kearwood/arcade/base/drop-sheet.jpg

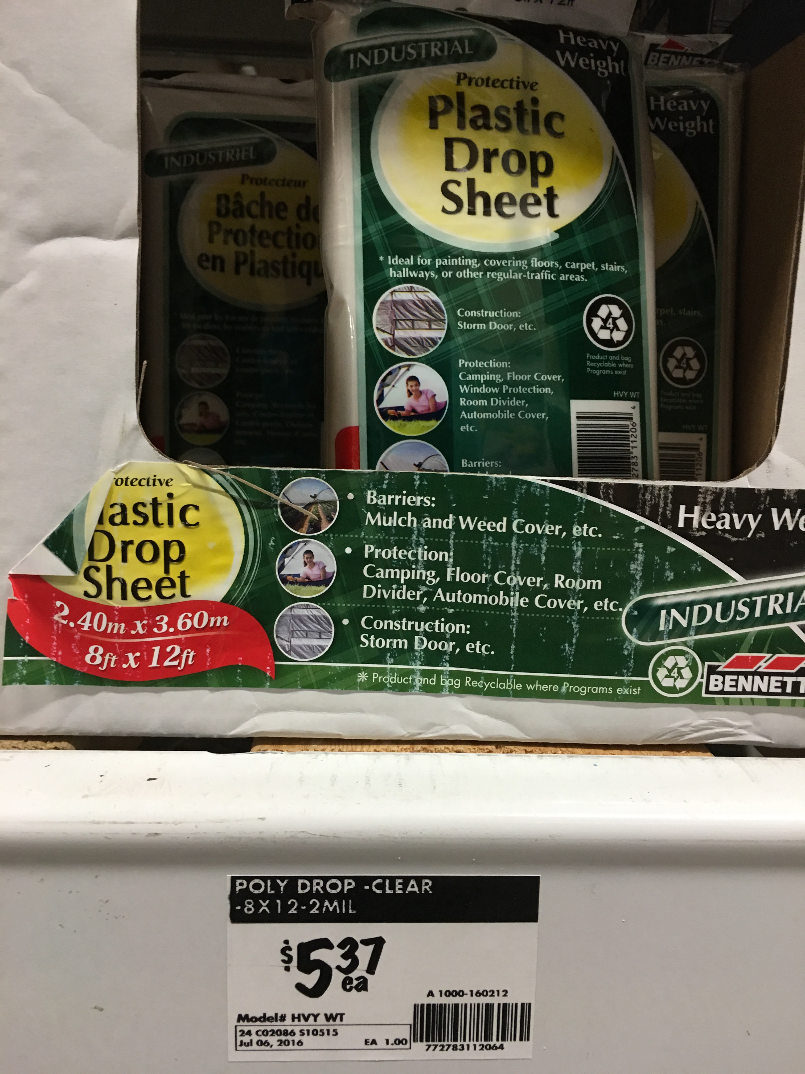
base/drop-sheet.jpg
