kearwood/arcade/base/laminate-pine.jpg

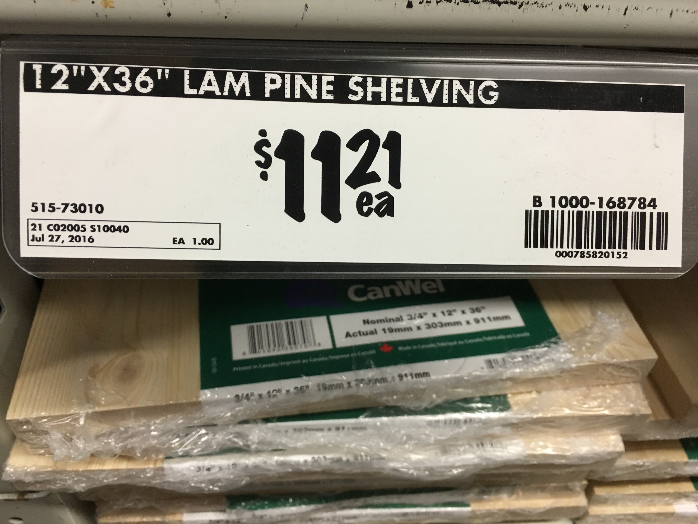
base/laminate-pine.jpg
