kearwood/arcade/base/minwax-polyurethane-clear-gloss.jpeg

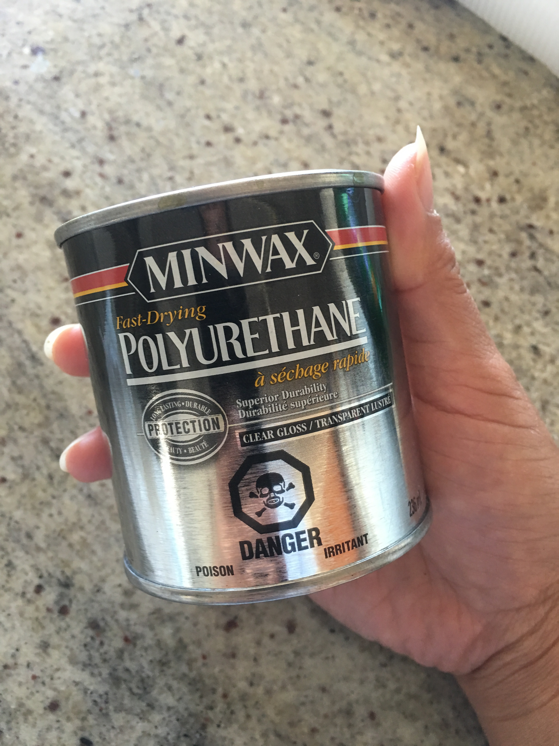
base/minwax-polyurethane-clear-gloss.jpeg
