kearwood/arcade/base/minwax-pre-stain-wood-conditioner.jpg

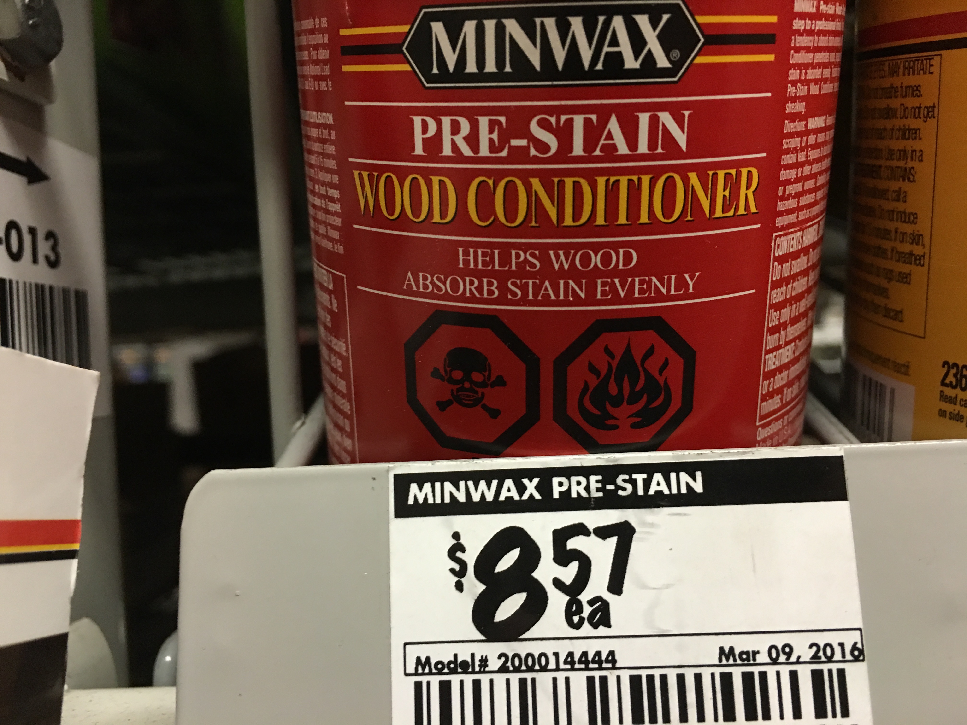
base/minwax-pre-stain-wood-conditioner.jpg
