kearwood/arcade/base/minwax-wood-stain-cherry-235.jpg

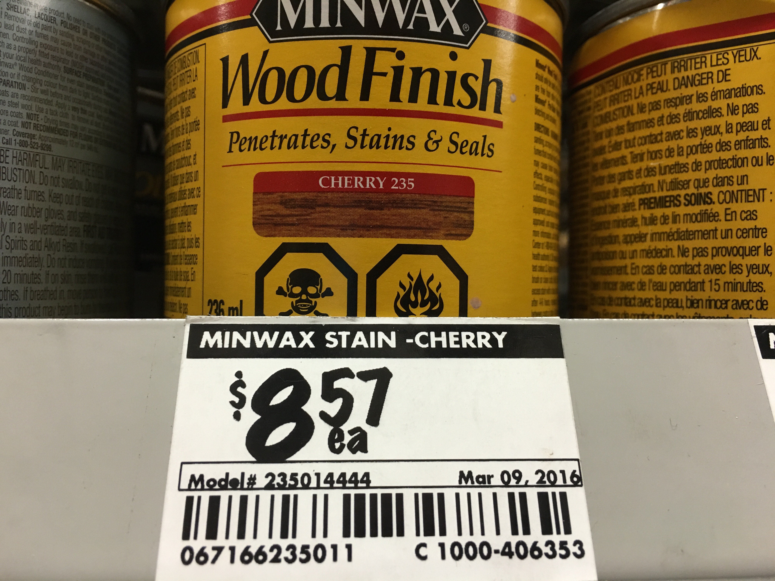
base/minwax-wood-stain-cherry-235.jpg
