kearwood/arcade/base/oak-sides.jpg

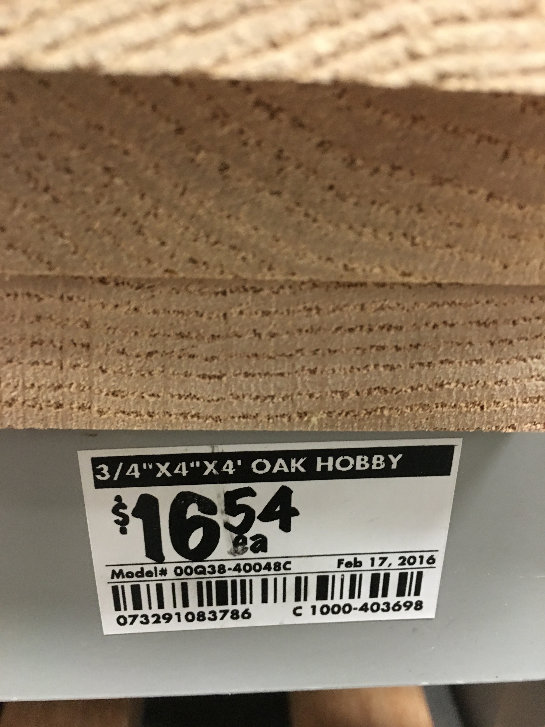
base/oak-sides.jpg
