kearwood/arcade/base/sanding-block.jpg

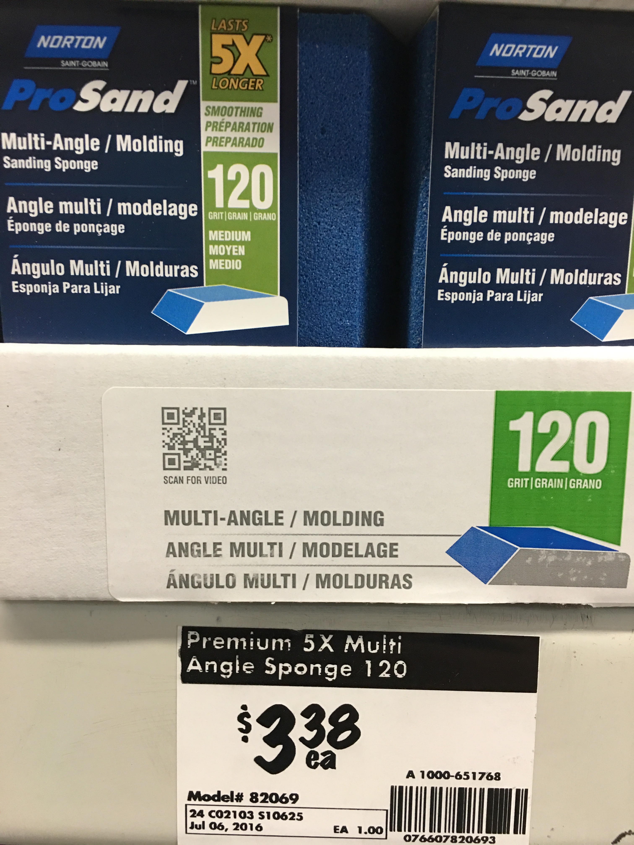
base/sanding-block.jpg
